mundodisco8/Snowflake/img/2032DischargeCurves.jpg

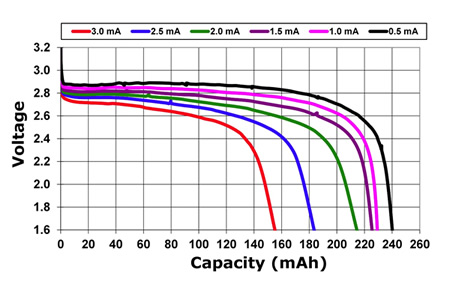
img/2032DischargeCurves.jpg
