mundodisco8/Snowflake/img/Astable_VoltageRef.png

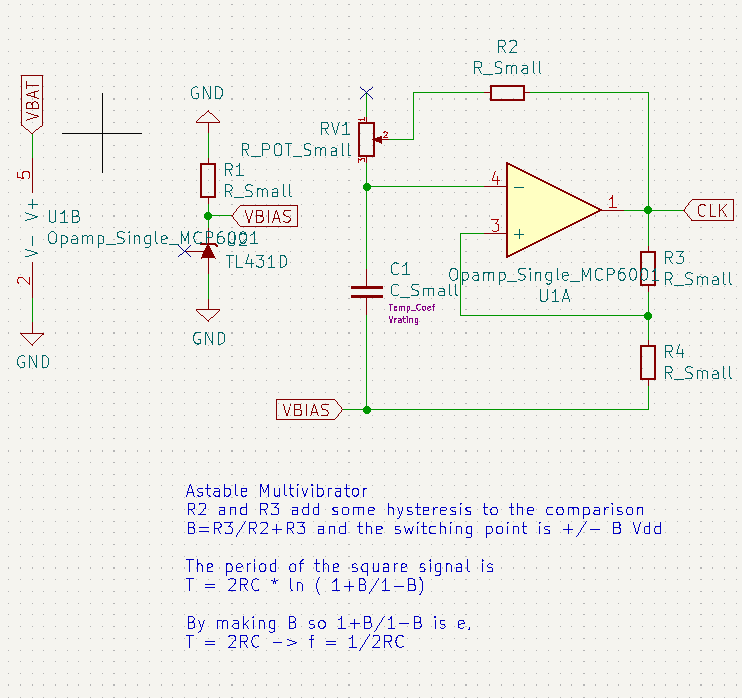
img/Astable_VoltageRef.png
