mundodisco8/Snowflake/img/Clock.png

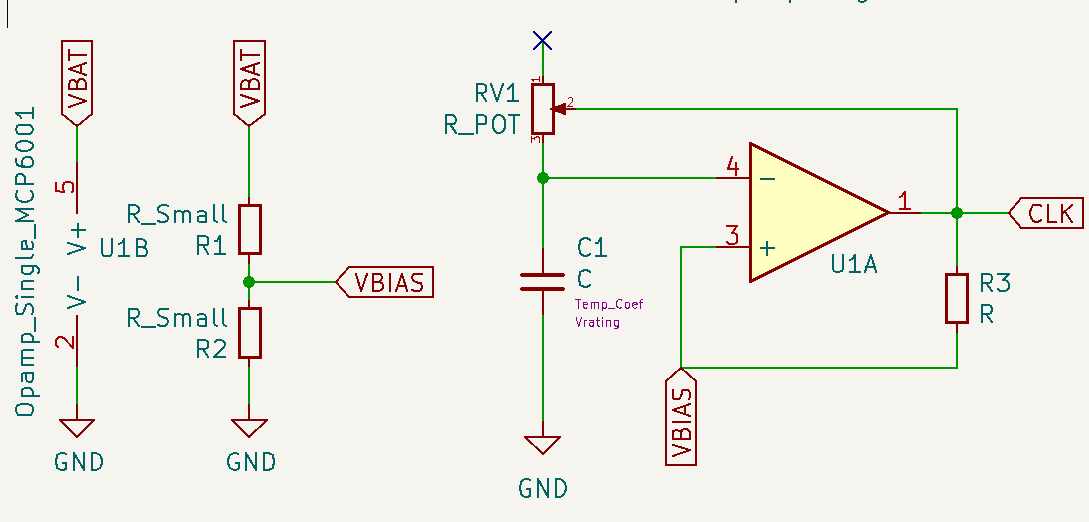
img/Clock.png
