mundodisco8/Snowflake/img/Counter.png

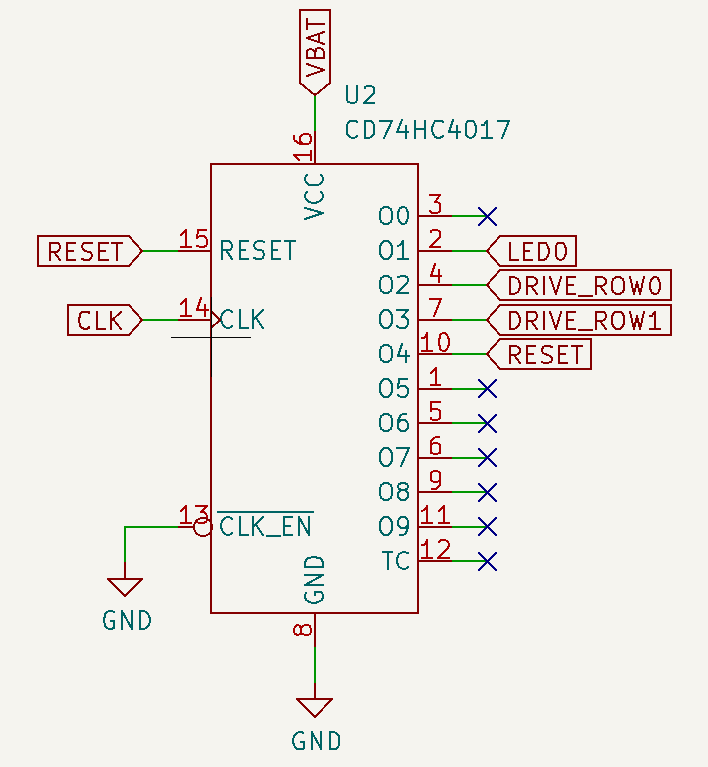
img/Counter.png
