mundodisco8/Snowflake/img/CR2032x1_On_PCB_Side.png

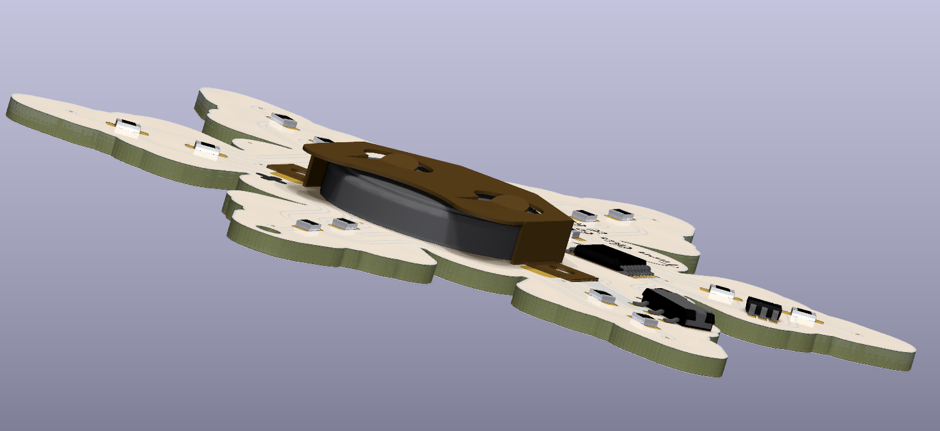
img/CR2032x1_On_PCB_Side.png
