mundodisco8/Snowflake/img/CR2032x2_On_PCB_Front.png

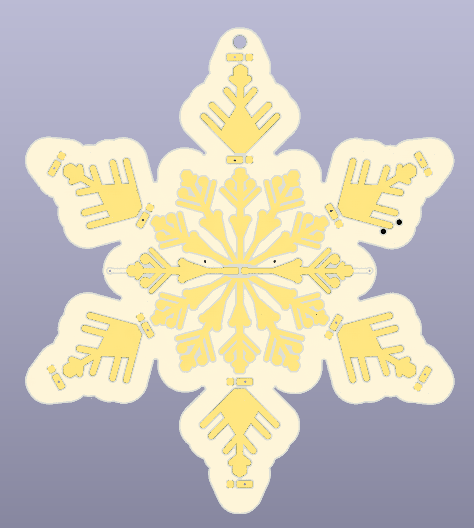
img/CR2032x2_On_PCB_Front.png
