mundodisco8/Snowflake/img/KW_DCLMS2_Bias.png

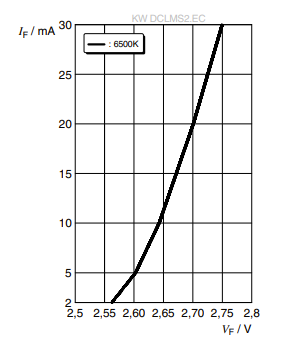
img/KW_DCLMS2_Bias.png
