mundodisco8/Snowflake/img/LTSPice.png

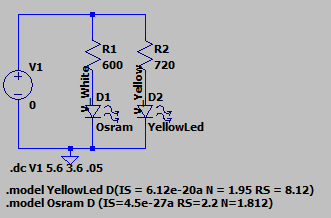
img/LTSPice.png
