mundodisco8/Snowflake/img/Schmitt_OutputHigh.png

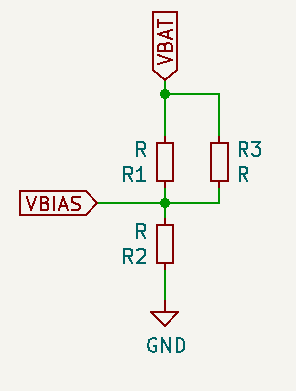
img/Schmitt_OutputHigh.png
