mundodisco8/Snowflake/img/Schmitt_OutputLow.png

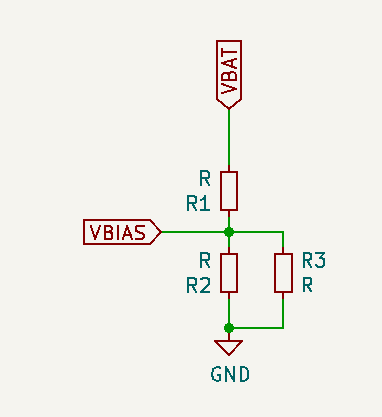
img/Schmitt_OutputLow.png
