mundodisco8/Snowflake/hardware/Snowflake_library/3D_Models/SOT23-5 v2.step

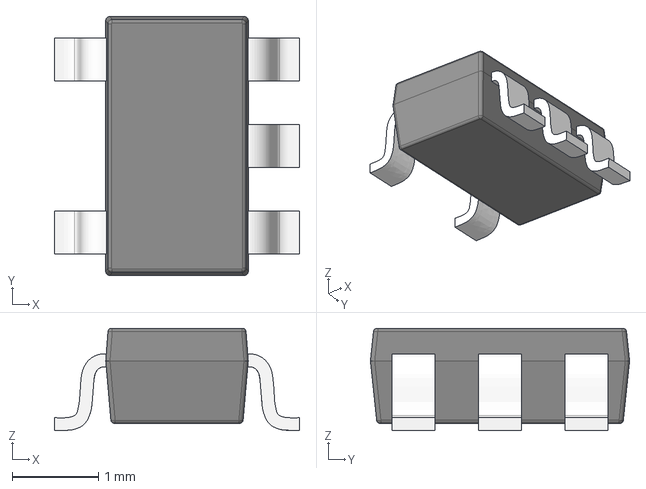
[picture p36: CAD file, 2019-12-10]
hardware/Snowflake_library/3D_Models/SOT23-5 v2.step
2.84 x 3.00 x 1.18 mm
