mundodisco8/Snowflake/hardware/Snowflake_library/3D_Models/14-SOIC Narrow 4x8.75x1.75mm Pitch 1.27mm v3.step

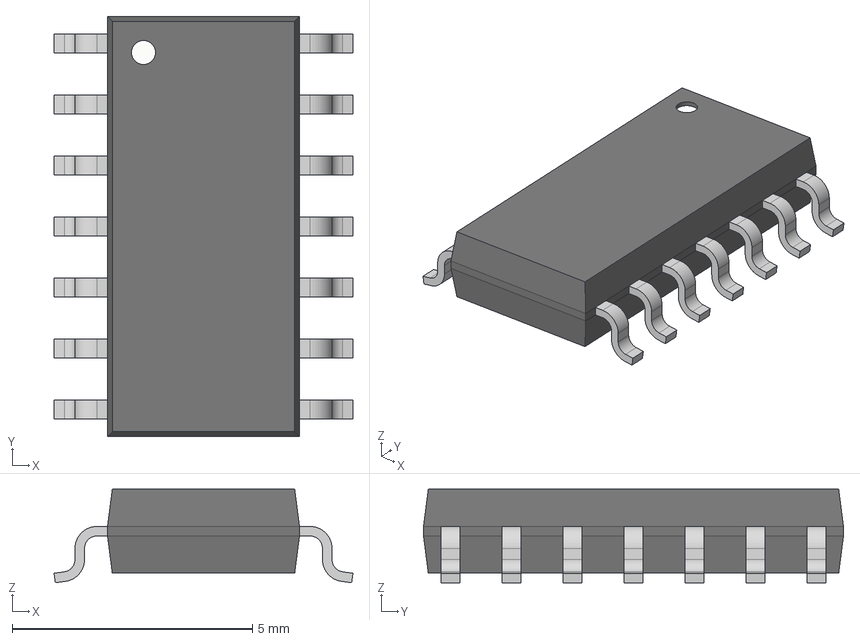
[picture p37: CAD file, 2019-12-10]
hardware/Snowflake_library/3D_Models/14-SOIC Narrow 4x8.75x1.75mm Pitch 1.27mm v3.step
6.23 x 8.75 x 1.95 mm
Pins x 7
Pins(Mirror) x 7
