mundodisco8/Snowflake/hardware/Snowflake_library/3D_Models/TC-33X-2 v2.step

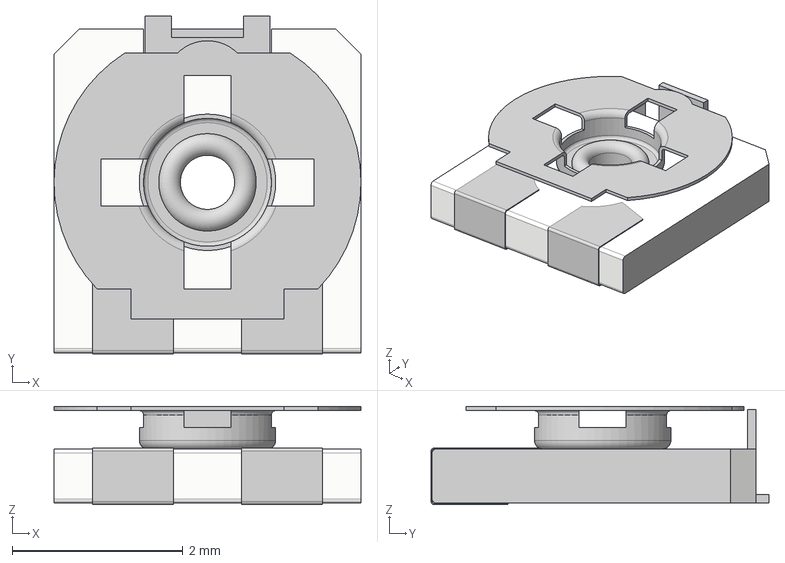
[picture p38: CAD file, 2019-12-10]
hardware/Snowflake_library/3D_Models/TC-33X-2 v2.step
3.60 x 3.96 x 1.15 mm
