mundodisco8/Snowflake/hardware/Snowflake_library/3D_Models/0606 - LED - 1.6x1.5mm v3.step

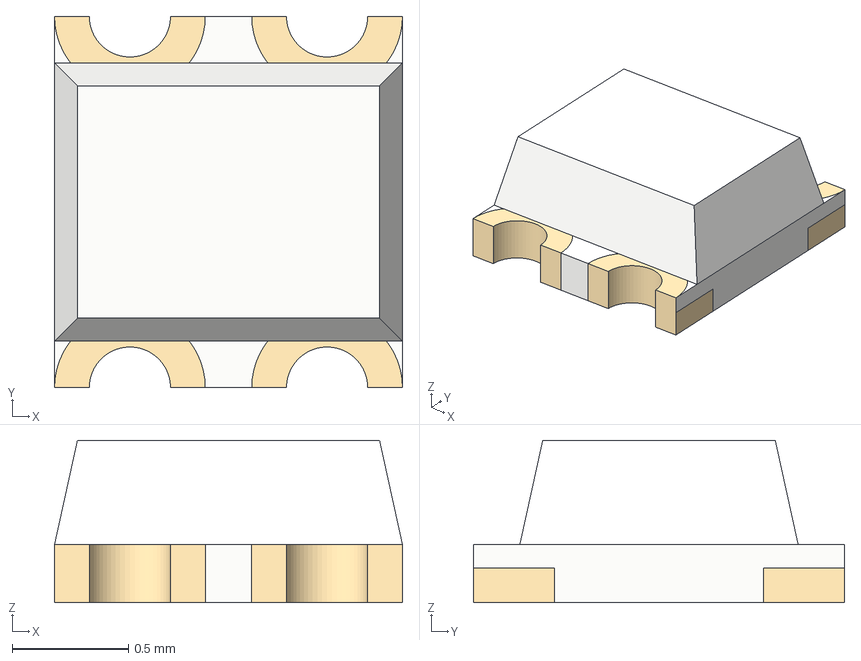
[picture p39: CAD file, 2019-12-06]
hardware/Snowflake_library/3D_Models/0606 - LED - 1.6x1.5mm v3.step
1.50 x 1.60 x 0.7 mm
Pins
LED Dome
