mundodisco8/Snowflake/hardware/Snowflake_library/3D_Models/0603 - LED v2.step

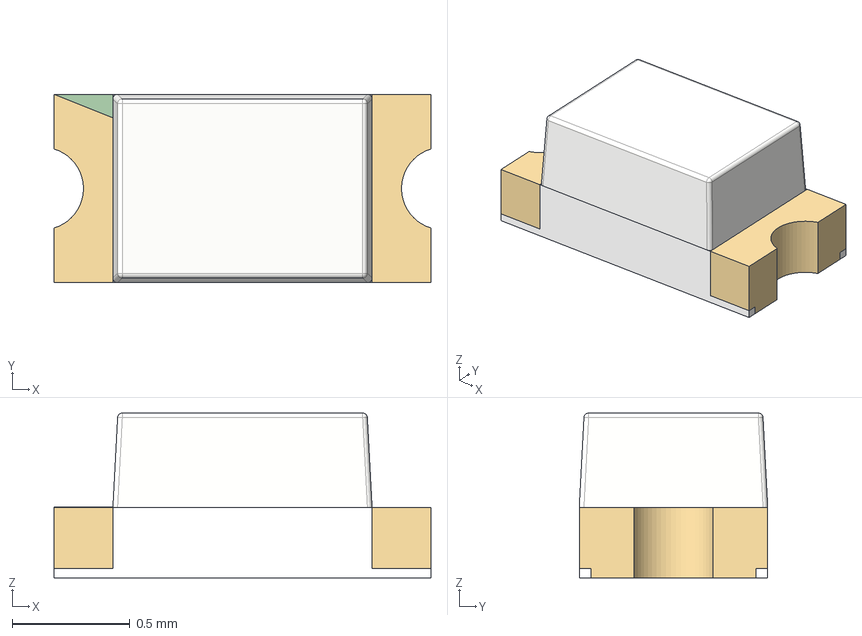
[picture p40: CAD file, 2019-12-06]
hardware/Snowflake_library/3D_Models/0603 - LED v2.step
1.60 x 0.8 x 0.7 mm
housing
cover
Polarity Mark
