mundodisco8/Snowflake/hardware/Snowflake_library/3D_Models/Resistor SMD 0805.step

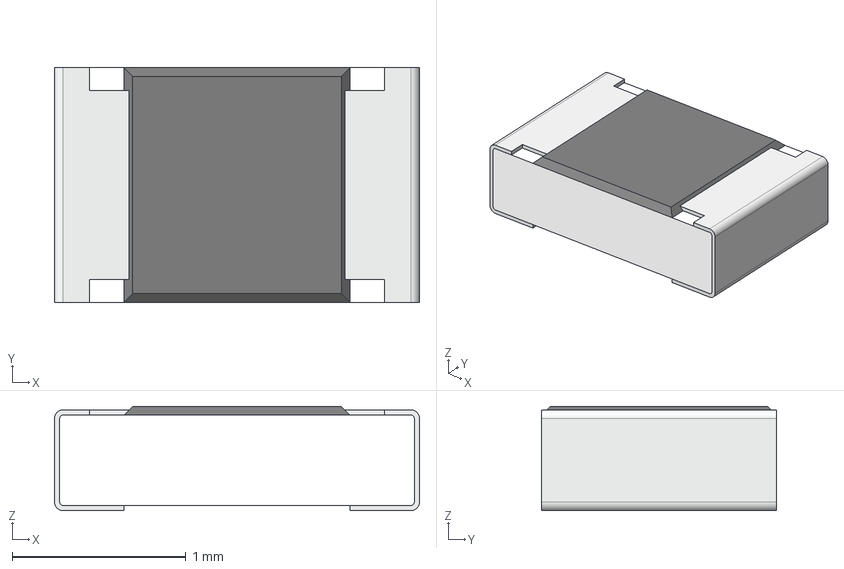
[picture p41: CAD file, 2019-12-06]
hardware/Snowflake_library/3D_Models/Resistor SMD 0805.step
2.10 x 1.35 x 0.6 mm
