mundodisco8/Snowflake/LTSpice/LED And Battery Sims.asc

D1: LED; Osram
D2: LED; YellowLed
R1: res; 40
R2: res; 160
V1: voltage; 0
Named nets: 0, V_White, V_Yellow
.dc V1 2.8 1.8 .05
.model YellowLed D(IS = 6.12e-20a N = 1.95 RS = 8.12)
.model Osram D (IS=4.5e-27a RS=2.2 N=1.812)
